rajinthanr/Attendance-Management-System/Presentation/Attendance_Management_System.pdf

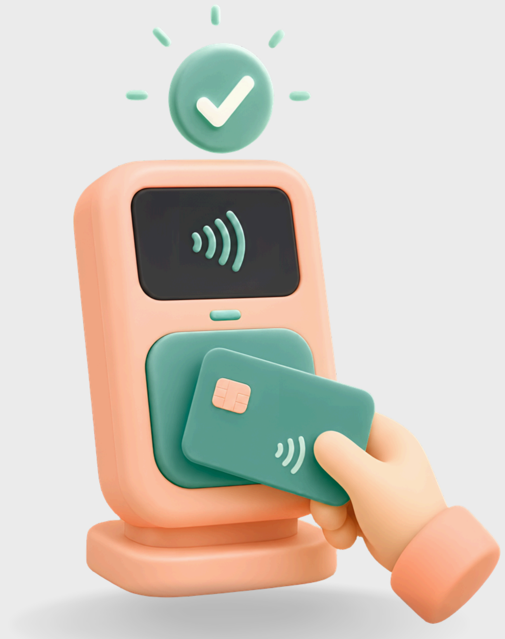
[picture p8: figure]

Rajinthan R. 220502M
Praveen V.V.J. 220491B
Sulojan R. 220626V

# Attendance Management System

### Group 05

# How System Works

Automate the process of taking attendance in live physical classes. A handheld NFC reader records each student card and the time.

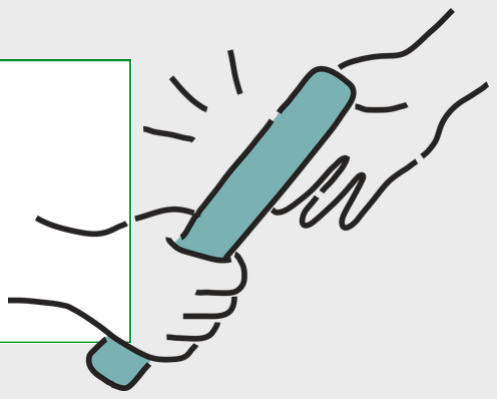
[picture p9: figure]
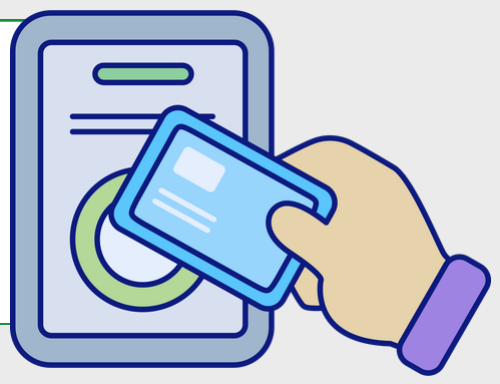
[picture p10: figure]

Pass the Reader

01

Tap the Student ID

02

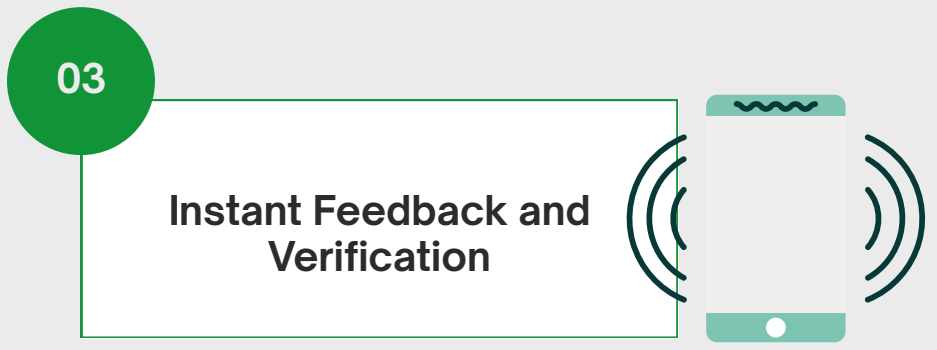
[picture p11: figure]
Instant Feedback and Verification
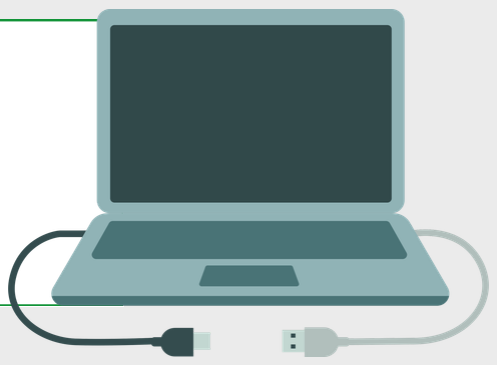
[picture p12: figure]

Plug in Over USB to
retrieve records

04

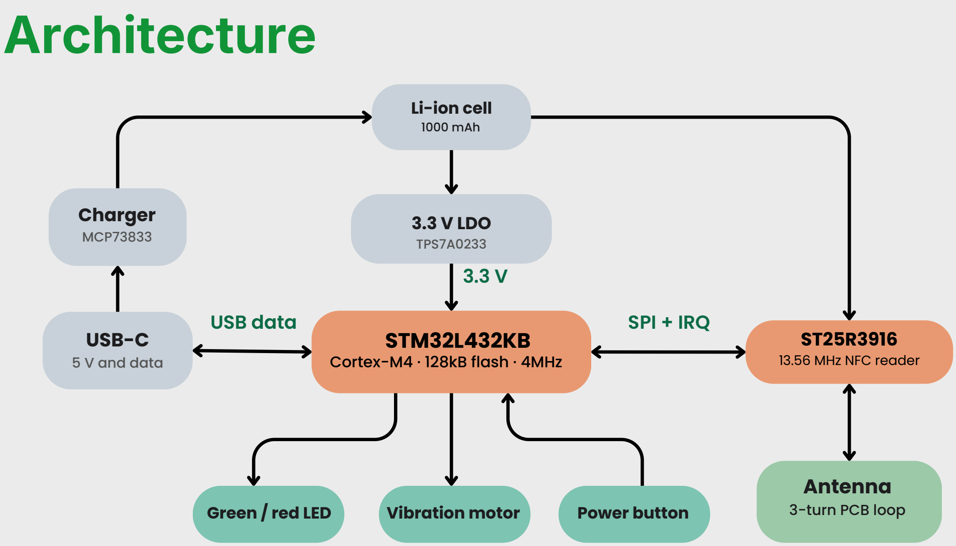
[picture p13: figure]
Green / red LED; Vibration motor; Power button; STM32L432KB Cortex-M4 · 128kB flash · 4MHz; ST25R3916 13.56 MHz NFC reader; USB-C 5 V and data; Charger MCP73833; Li-ion cell 1000 mAh; 3.3 V LDO TPS7A0233; Architecture; Antenna 3-turn PCB loop; USB data; SPI + IRQ

# Power Analysis

1.8 µA | 108 µA | 2.8µAh | 17 months

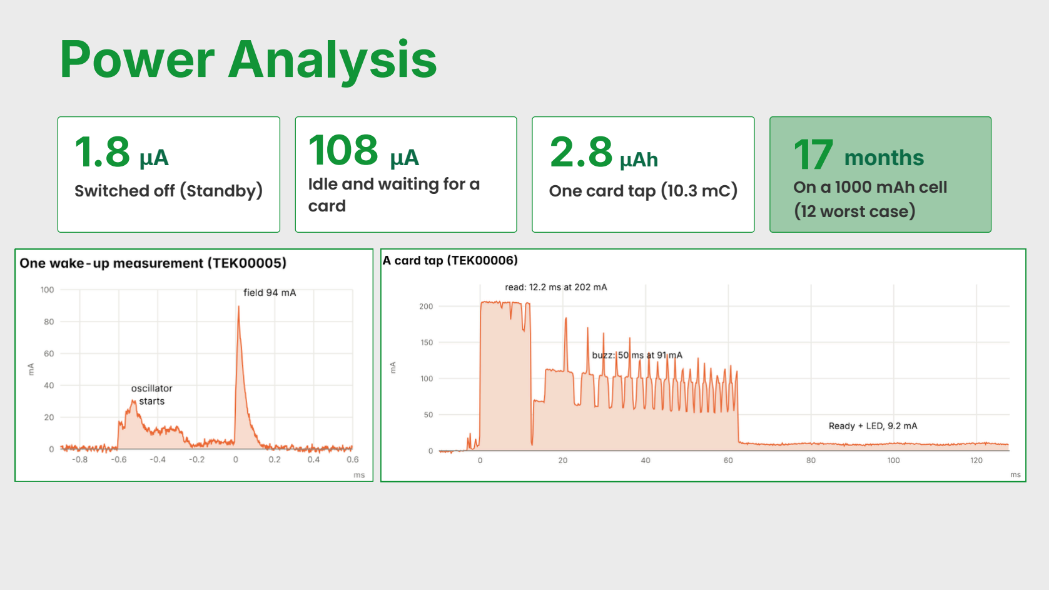
[picture p14: page 4]

Switched off (Standby)

Idle and waiting for a
card

One card tap (10.3 mC) On a 1000 mAh cell (12 worst case)

# Idle Scanning

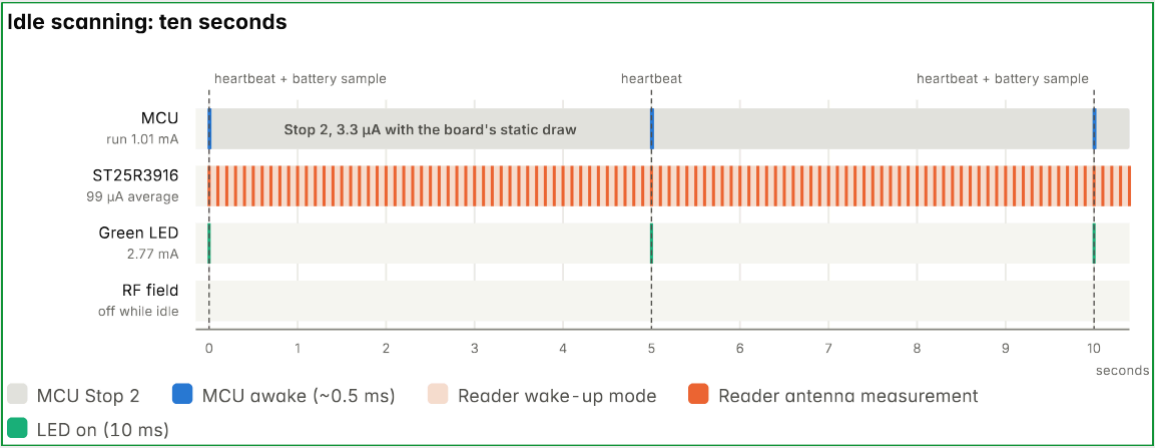
[picture p15: figure]

# One card Tap

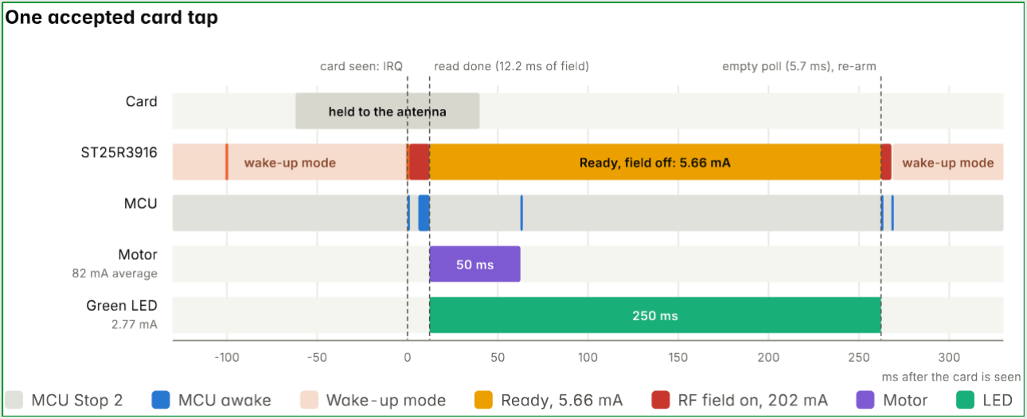
[picture p16: figure]

# Clock Speed Calculation

Clock | Speed | Why
Scanning | 4 MHz (MSI) | no PLL to relock on each wake-up

USB
session

RTC,
timers

Reader
SPI

USB clock

HSI48 +
CRS

32.768
kHz

### 24 MHz

(MSI)

500 kHz chip allows 10 MHz

USB needs above 14.2
MHz; power comes from
the cable

locks to the host, no
crystal

runs through sleep for
under 1 µA

## Chargein one 15 ms card read

MCU at 4 MHz
(chosen)
MCU at 24 MHz
MCU at 80 MHz
(PLL)
RF field for the
same read

### Reading a card waits on the radio, not on the processor, so the slowest clock that meets the timing wins. At 4 MHz the MCU is under 1 % of a

read.

### 42 µC

135 µC

### 15.2 µC

2030 µC

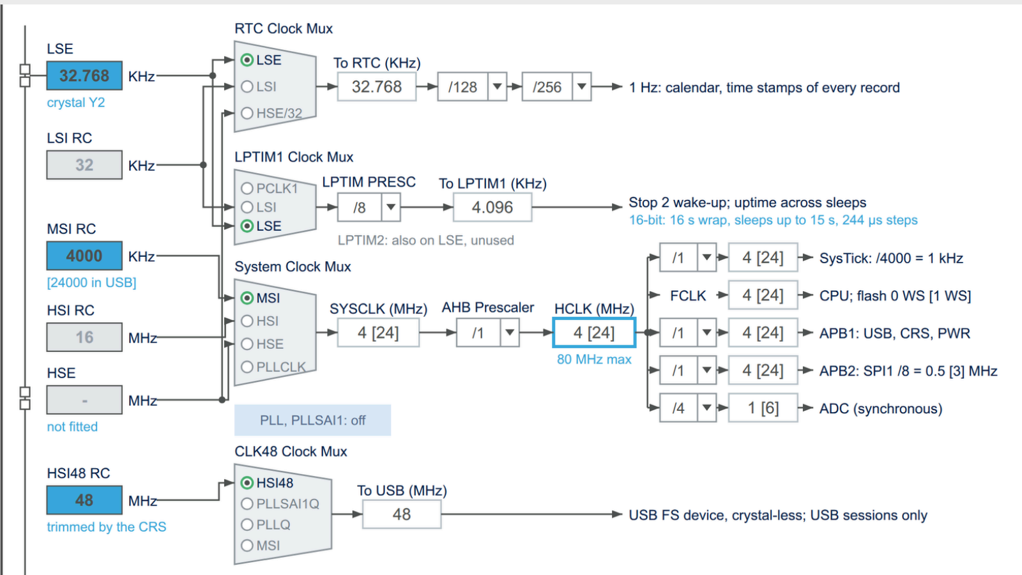
[picture p17: page 8]

# Memory

### Program: 36 pages, 72 kB

### One record is 8 bytes: card number and time. That is exactly one flash double-

word.

### A page holds 254 records. 6,858 records is

about 64 lectures of 100 students.

### The log fills in about 16 teaching days. The

app clears it each time a lecture starts.

## STM32L432KB: 128kB of flash, 64 pages of 2 kB

### Attendance log: 27 pages

image 60.6 kB at -Og, 11.4 kB free | 6,858records
program | config page (device ID) | log

Build
Debug (-Og)
Release (-Os)

Image

### 62.1 kB

### 51.5 kB

Fits 72 kB
yes, 11.4 kB free
yes, 21.7 kB free

# Justification of NFC

Cards

Reader

discrete
circuit

First design
125 kHz
EM4100

EM4100 tags

one chip

ISO 14443-A
cards

Final

### 13.56 MHz NFC

18.2mA | 194µA
polling the reader all the time(125 kHz) | with the reader's wake-up mode

### Student ID cards and NFC tags are usually 13.56 MHz. One reader IC, the ST25R3916, reads them

over SPI.
Every card has its own number (4, 7 or 10 bytes). That number is all the device stores.

### The reader can look for a card by itself every 100

ms while the MCU sleeps.

### The antenna is a 3-turn loop etched on the PCB:

no extra part.

# PCB Design

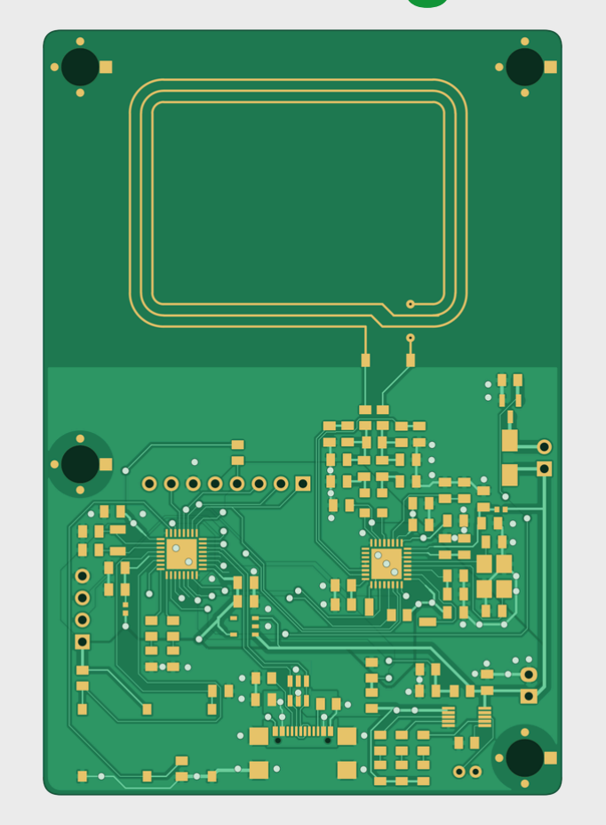
[picture p18: figure]

Block

MCU

NFC reader

Charger

LDO

USB protection

Part

STM32L432KB

ST25R3916

MCP73833

TPS7A0233

USBLC6-2SC6

loop antenna etched on the board, 3 turns.

## USB-C at the bottom edge charges the cell and shows

the drive.

## Reader and motor run straight from the cell; the MCU

from a 3.3 V LDO.

# The Companion App

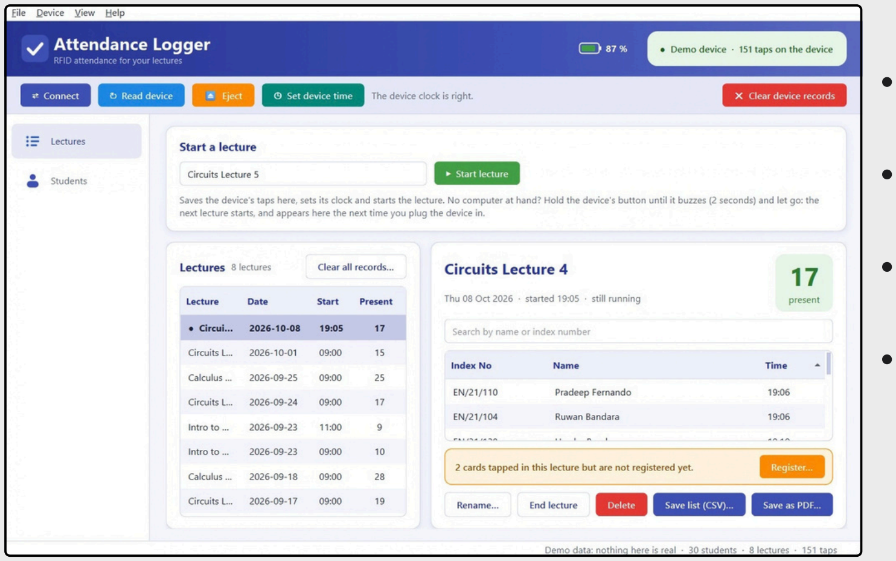
[picture p19: figure]

## Plug the device in and the app

reads every tap.
See who came: index number, name, time.

## Save each lecture as CSV or

PDF.

## Register new cards from the

device.

# Total Cost

Units made | 1 | 100 | 1,000 | 10,000
Cost per unit (USD) | 227.62 | 32.43 | 25.40 | 18.31
Cost per unit (LKR) | 75,115 | 10,702 | 8,382 | 6,042

## Where $25.40 goes (1,000 units)

Electronic parts
Battery, motor, case
Import duty, VAT, levies
PCB and assembly
Test, freight, yield loss

$11.20
$6.70
$4.80
$0.96
$1.74

# Quick Guide

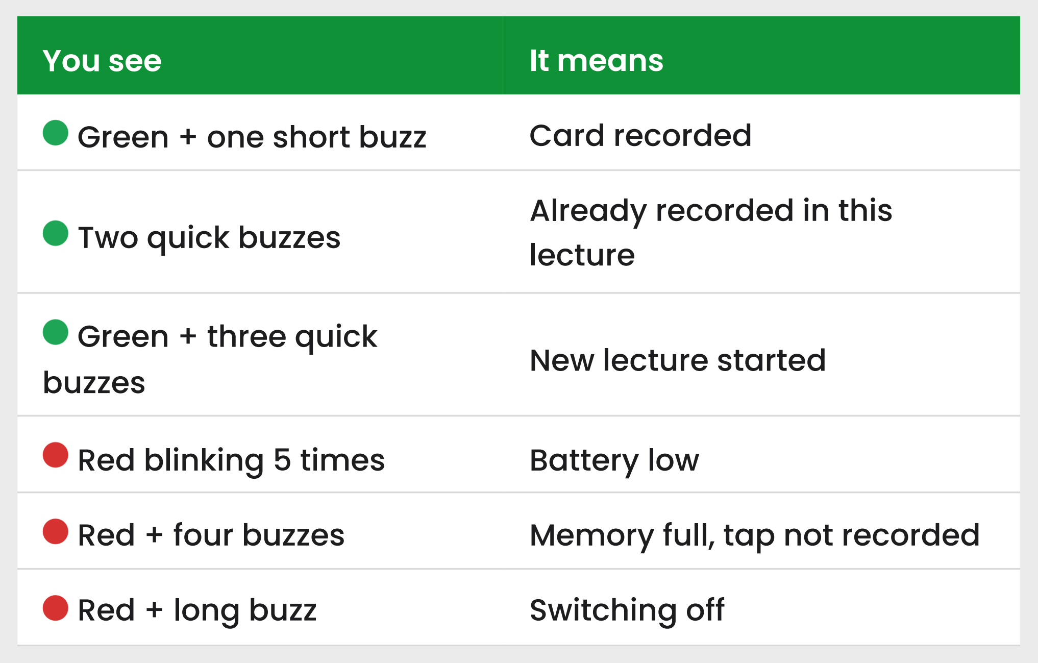
[picture p20: figure]
Two quick buzzes; Green + three quick buzzes; Red blinking 5 times; Red + four buzzes; Red + long buzz; You see; Green + one short buzz; New lecture started; It means; Card recorded; Already recorded in this lecture; Battery low; Memory full, tap not recorded; Switching off

Press (off)

Tap

Hold 2 s

Hold 5 s

Switch on

Show the battery

Start next lecture

Switch off

The power button

It switches itself off after 3 minutes without a tap. Records are kept.

1 Switch on; 2 Tap cards; 3 Hold 2 s for the next lecture; 4 Plug in, open the app
