rajinthanr/Attendance-Management-System/Presentation/Why_4MHz.pdf

# Why 4 MHz?

The radio sets the pace: run slow, wake fast, sleep.

MCU charge per read (15 ms awake)
2 MHz | 12 µC
4 MHz | 15 µC
24 MHz | 42 µC
80 MHz | 135 µC
RF field | 2,030 µC

### 2 MHz vs 4 MHz, SPI 500 kHz in both

MCU job
4 MHz | 0.51 µC
2 MHz | 0.83 µC
+65 % at 2 MHz

ADC sample
4 MHz | 1.81 µC
2 MHz | 3.09 µC
+70 % at 2 MHz

Card read
4 MHz | 2.47 mC
2 MHz | 3.00 mC
+21 % at 2 MHz

12µs

wake-up from Stop 2, no PLL
99.965 %

of idle time asleep
0.4 %

of idle current is the MCU running

IRQ priority: USB 5 · reader, button, LPTIM 6 · SysTick 15

4 MHz measured; 24/80 MHz datasheet; 2 MHz estimated. At 2 MHz the code takes twice as long, so the 202 mA field stays on longer.
