rajinthanr/Attendance-Management-System/PCB/Attendance Management System.pdf

Attendance Management System

Reference | Qty Value | DNP
AE1,AE2 | 2 Antenna
C1,C3,C8,C11,C22,C23,C24,C25,C28,C29,C30,C34 | 12 100n
C2,C35 | 2 4.7u
C4 | 1 10n
C5,C33 | 2 1u
C6,C7 | 2 4.3p
C9,C10 | 2 15p
C12,C13 | 2 150p
C14,C15 | 2 100p
C16,C17 | 2 68p
C18,C19 | 2 270p
C20,C21,C36 | 3 10u
C26,C27,C31,C32 | 4 2.2u
D1,D5 | 2 RED
D2,D3,D6 | 3 GREEN
D4 | 1 SS14
FB1,FB2 | 2 600R@100MHz
J1 | 1 USB-C
J2 | 1 BATTERY
J3 | 1 SWD
J4 | 1 VIB_MOTOR
J5 | 1 CSO
J6 | 1 CSI
J7 | 1 PN532
L3,L4 | 2 470nH
Q1 | 1 AO3400A
R1,R2 | 2 5.1k
R3,R4,R5,R9,R10 | 5 470R
R6,R13,R14 | 3 1k
R7,R8,R11,R12,R20 | 5 10k
R15 | 1 1.5k
R16,R18,R19 | 3 4.7M
R17 | 1 2.7M
SW1 | 1 RST
SW2 | 1 BOOT0
SW3 | 1 POWER
TH1 | 1 10k NTC
U1 | 1 STM32L432KCUx
U2 | 1 MCP73833-xxx-UN
U3 | 1 TPS7A0233PDBVR
U5 | 1 ST25R3916-AQWT
U6 | 1 USBLC6-2SC6
Y1 | 1 27.12MHz
Y2 | 1 32.768k

Exclude from BOM Exclude from Board Exclude from Simulation Exclude from Position Files ${EXCLUDE_FROM_POS_FILES}
${EXCLUDE_FROM_POS_FIL
${EXCLUDE_FROM_POS_FIL
${EXCLUDE_FROM_POS_FIL
${EXCLUDE_FROM_POS_FIL
${EXCLUDE_FROM_POS_FIL
${EXCLUDE_FROM_POS_FIL
${EXCLUDE_FROM_POS_FIL
${EXCLUDE_FROM_POS_FIL
${EXCLUDE_FROM_POS_FIL
${EXCLUDE_FROM_POS_FIL
${EXCLUDE_FROM_POS_FIL
${EXCLUDE_FROM_POS_FIL
${EXCLUDE_FROM_POS_FIL
${EXCLUDE_FROM_POS_FIL
${EXCLUDE_FROM_POS_FIL
${EXCLUDE_FROM_POS_FIL
${EXCLUDE_FROM_POS_FIL
${EXCLUDE_FROM_POS_FIL
${EXCLUDE_FROM_POS_FIL
${EXCLUDE_FROM_POS_FIL
${EXCLUDE_FROM_POS_FIL
${EXCLUDE_FROM_POS_FIL
${EXCLUDE_FROM_POS_FIL
${EXCLUDE_FROM_POS_FIL
${EXCLUDE_FROM_POS_FIL
${EXCLUDE_FROM_POS_FIL
${EXCLUDE_FROM_POS_FIL
${EXCLUDE_FROM_POS_FIL
${EXCLUDE_FROM_POS_FIL
${EXCLUDE_FROM_POS_FIL
${EXCLUDE_FROM_POS_FIL
${EXCLUDE_FROM_POS_FIL
${EXCLUDE_FROM_POS_FIL
${EXCLUDE_FROM_POS_FIL
${EXCLUDE_FROM_POS_FIL
${EXCLUDE_FROM_POS_FIL
${EXCLUDE_FROM_POS_FIL
${EXCLUDE_FROM_POS_FIL
${EXCLUDE_FROM_POS_FIL
${EXCLUDE_FROM_POS_FIL
${EXCLUDE_FROM_POS_FIL
${EXCLUDE_FROM_POS_FIL
${EXCLUDE_FROM_POS_FIL

Footprint

Capacitor_SMD:C_0805_2012Metric Capacitor_SMD:C_0805_2012Metric Capacitor_SMD:C_0805_2012Metric Capacitor_SMD:C_0805_2012Metric Capacitor_SMD:C_0805_2012Metric Capacitor_SMD:C_0805_2012Metric Capacitor_SMD:C_0805_2012Metric Capacitor_SMD:C_0805_2012Metric Capacitor_SMD:C_0805_2012Metric Capacitor_SMD:C_0805_2012Metric Capacitor_SMD:C_0805_2012Metric Capacitor_SMD:C_0805_2012Metric LED_SMD:LED_0805_2012Metric LED_SMD:LED_0805_2012Metric Diode_SMD:D_SMA
Inductor_SMD:L_0402_1005Metric Connector_USB:USB_C_Receptacle_GCT_USB4110 Connector_JST:JST_XA_B02B-XASK-1_1x02_P2.50mm_Vertical Connector_PinHeader_2.54mm:PinHeader_1x04_P2.54mm_Vertical Connector_PinHeader_2.54mm:PinHeader_1x02_P2.54mm_Vertical Connector_Wire:SolderWirePad_1x01_SMD_1x2mm Connector_Wire:SolderWirePad_1x01_SMD_1x2mm Connector_PinSocket_2.54mm:PinSocket_1x08_P2.54mm_Vertical Inductor_SMD:L_0402_1005Metric
Package_TO_SOT_SMD:SOT-23
Resistor_SMD:R_0805_2012Metric Resistor_SMD:R_0805_2012Metric Resistor_SMD:R_0805_2012Metric Resistor_SMD:R_0805_2012Metric Resistor_SMD:R_0805_2012Metric
Resistor_SMD:R_0805_2012Metric
Resistor_SMD:R_0805_2012Metric Button_Switch_SMD:SW_Tactile_SPST_NO_Straight_CK_PTS636Sx25SMTRLFS Button_Switch_SMD:SW_Tactile_SPST_NO_Straight_CK_PTS636Sx25SMTRLFS Button_Switch_SMD:SW_Tactile_SPST_NO_Straight_CK_PTS636Sx25SMTRLFS Resistor_THT:R_Axial_DIN0204_L3.6mm_D1.6mm_P1.90mm_Vertical Package_DFN_QFN:QFN-32-1EP_5x5mm_P0.5mm_EP3.45x3.45mm Package_SO:MSOP-10_3x3mm_P0.5mm
External:SOT23_DBV_TEX-L
External:QFN50P500X500X100-33N Package_TO_SOT_SMD:SOT-23-6 Crystal:Crystal_SMD_3225-4Pin_3.2x2.5mm_HandSoldering Crystal:Crystal_SMD_EuroQuartz_EQ161-2Pin_3.2x1.5mm

Datasheet

https://www.vishay.com/docs/88746/ss12.pdf

https://www.usb.org/sites/default/files/documents/usb_type-c.zip

http://www.aosmd.com/pdfs/datasheet/AO3400A.pdf

https://www.st.com/resource/en/datasheet/stm32l432kc.pdfhttps://ww1.microchip.com/downloads/aemDocuments/documents/OTH/ProductDocuments/DataSheets/22005b.pdfhttps://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

https://www.st.com/resource/en/datasheet/usblc6-2.pdf
