rajinthanr/Attendance-Management-System/Firmware/Tests/test_session.c

/**
 * @file    test_session.c
 * @brief   Host tests for lecture sessions: the marker format, the in-session
 *          duplicate check, how markers are hidden in ATTEND.CSV, and starting
 *          a session over USB.
 */
#include <stdlib.h>
#include "test_util.h"
#include "test_hostfs.h"

#include "csv.h"
#include "device_cfg.h"
#include "session.h"
#include "log_store.h"
#include "record_buffer.h"
#include "settings_file.h"
#include "timeutil.h"
#include "usb_storage.h"

static log_store_t     g_ls;
static record_buffer_t g_rb;
static hostfs_t        g_hf;

static const app_datetime_t k_now = { 2026u, 9u, 10u, 13u, 27u, 45u };

static void flush_all(void)
{
    (void)log_flush(&g_ls, &g_rb);
}

static void add(uint32_t id, uint32_t stamp)
{
    app_record_t r;

    r.student_id = id;
    r.stamp = stamp;
    if (rb_count(&g_rb) >= (APP_RAM_RECORDS - SESS_MAX_RECORDS)) {
        flush_all();
    }
    (void)rb_push(&g_rb, &r);
}

static void mark(const char *module, const char *lecture, uint32_t stamp)
{
    app_record_t recs[SESS_MAX_RECORDS];
    uint16_t n = sess_encode(recs, SESS_MAX_RECORDS, stamp, module, lecture);
    uint16_t i;

    if (rb_count(&g_rb) >= (APP_RAM_RECORDS - SESS_MAX_RECORDS)) {
        flush_all();
    }
    for (i = 0u; i < n; i++) {
        (void)rb_push(&g_rb, &recs[i]);
    }
}

static void fresh(void)
{
    host_flash_erase_all();
    log_init(&g_ls);
    rb_init(&g_rb);
    host_set_time(&k_now);
}

/* ===================================================================== */
/* The marker format                                                      */
/* ===================================================================== */
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
